Multi-Volt/GG-PrintableMagnets/Data/Plots/10percent_trial1/10percent_trial1_vector_field_scalar.png

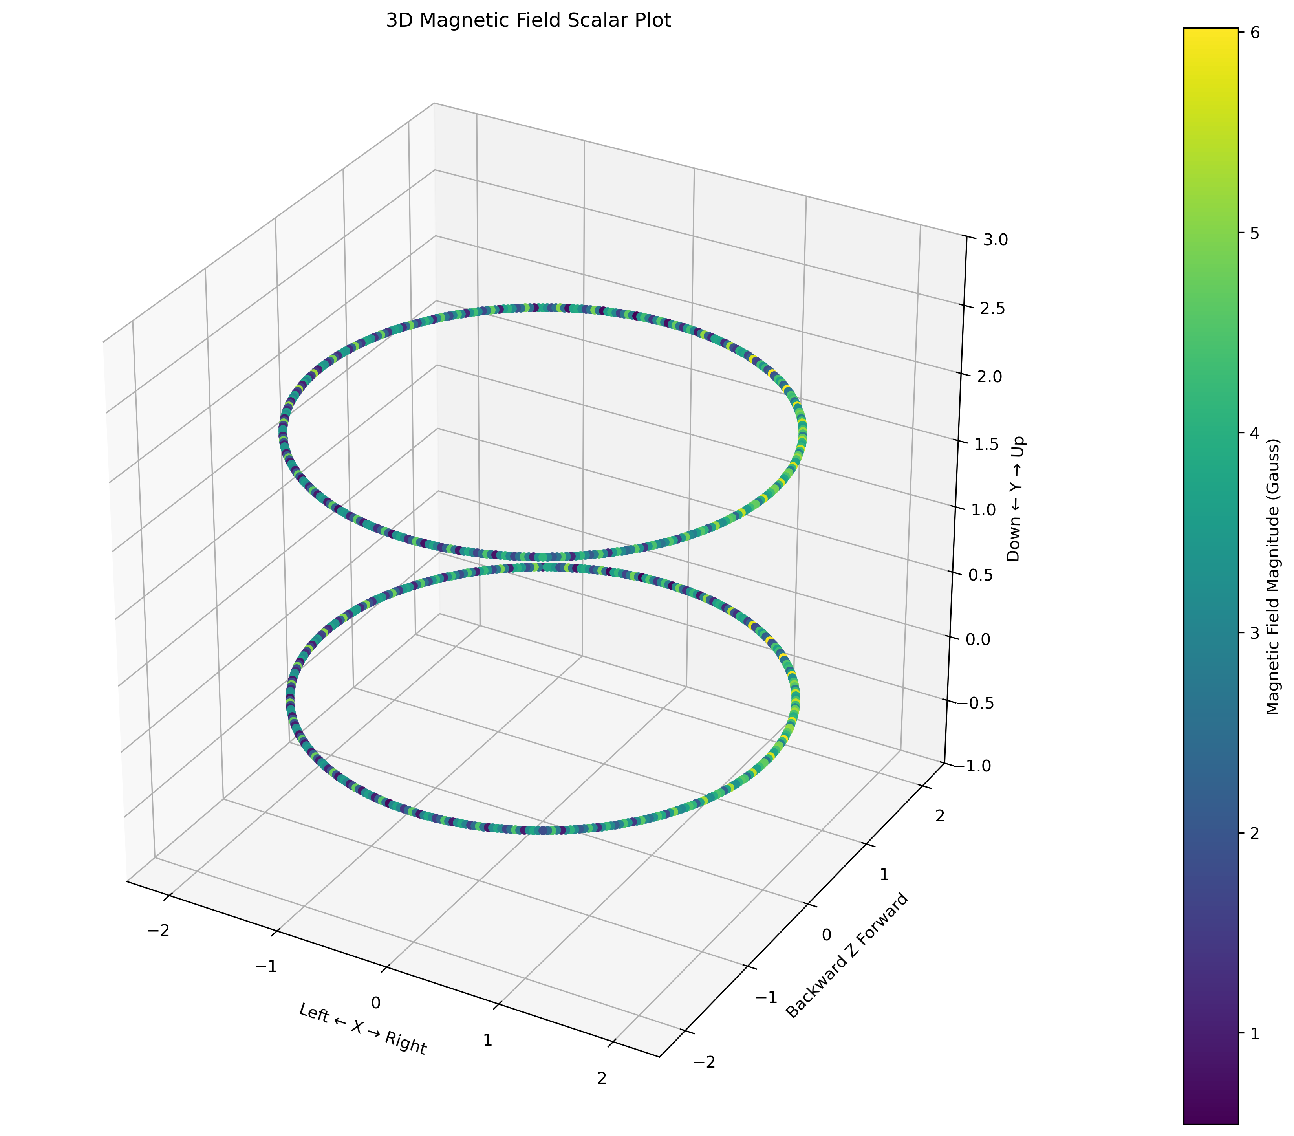
Data/Plots/10percent_trial1/10percent_trial1_vector_field_scalar.png
