Multi-Volt/GG-PrintableMagnets/Data/Plots/10percent_trial1/10percent_trial1_vector_field_true_vector.png

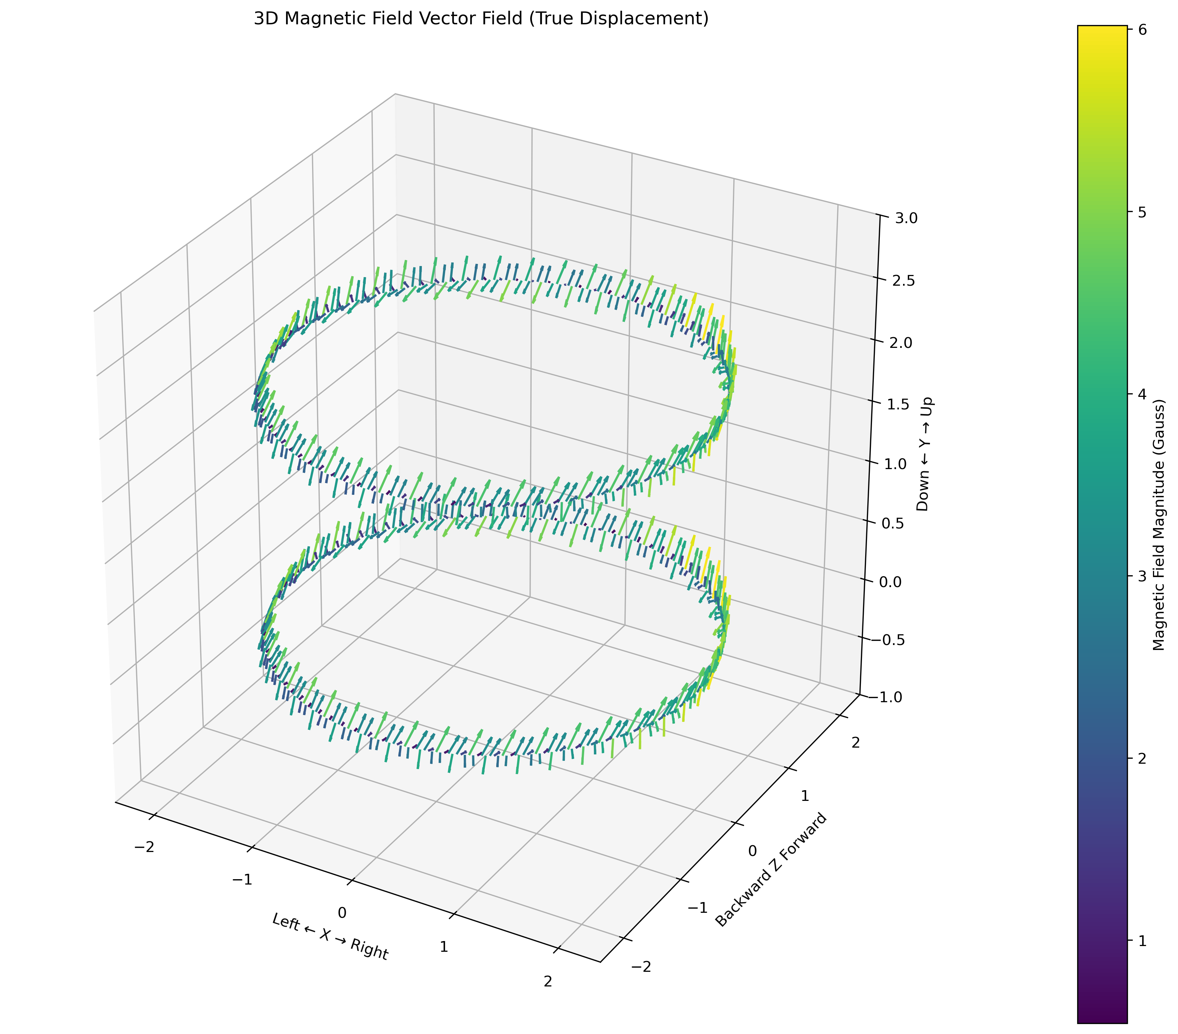
Data/Plots/10percent_trial1/10percent_trial1_vector_field_true_vector.png
