Multi-Volt/GG-PrintableMagnets/Data/Plots/10percent_trial2/10percent_trial2_vector_field_mesh_shrink.png

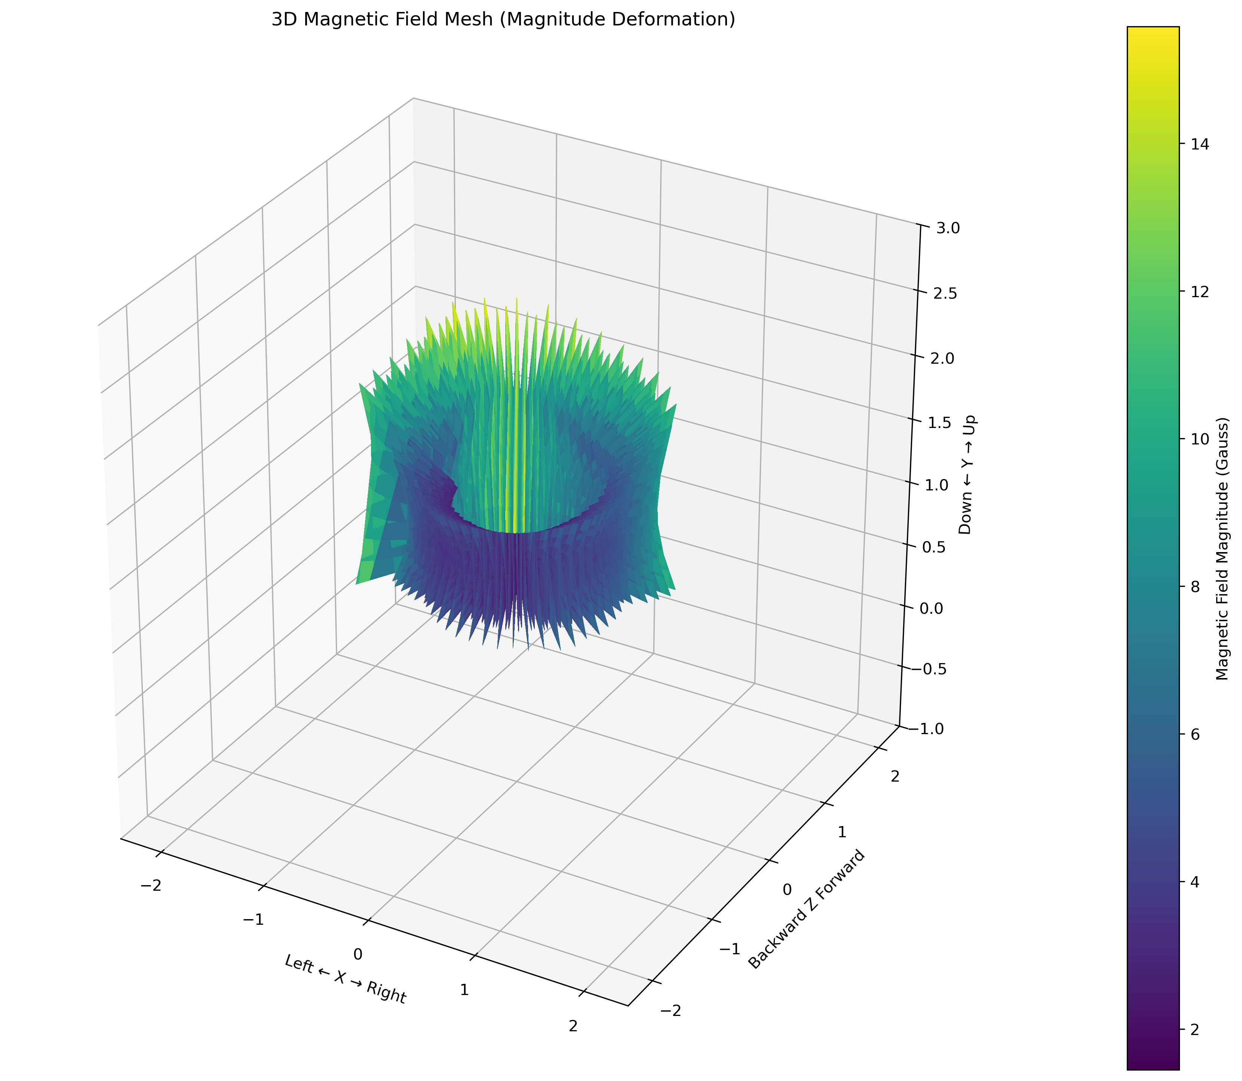
Data/Plots/10percent_trial2/10percent_trial2_vector_field_mesh_shrink.png
