Multi-Volt/GG-PrintableMagnets/Data/Plots/10percent_trial2/10percent_trial2_vector_field_true_vector.png

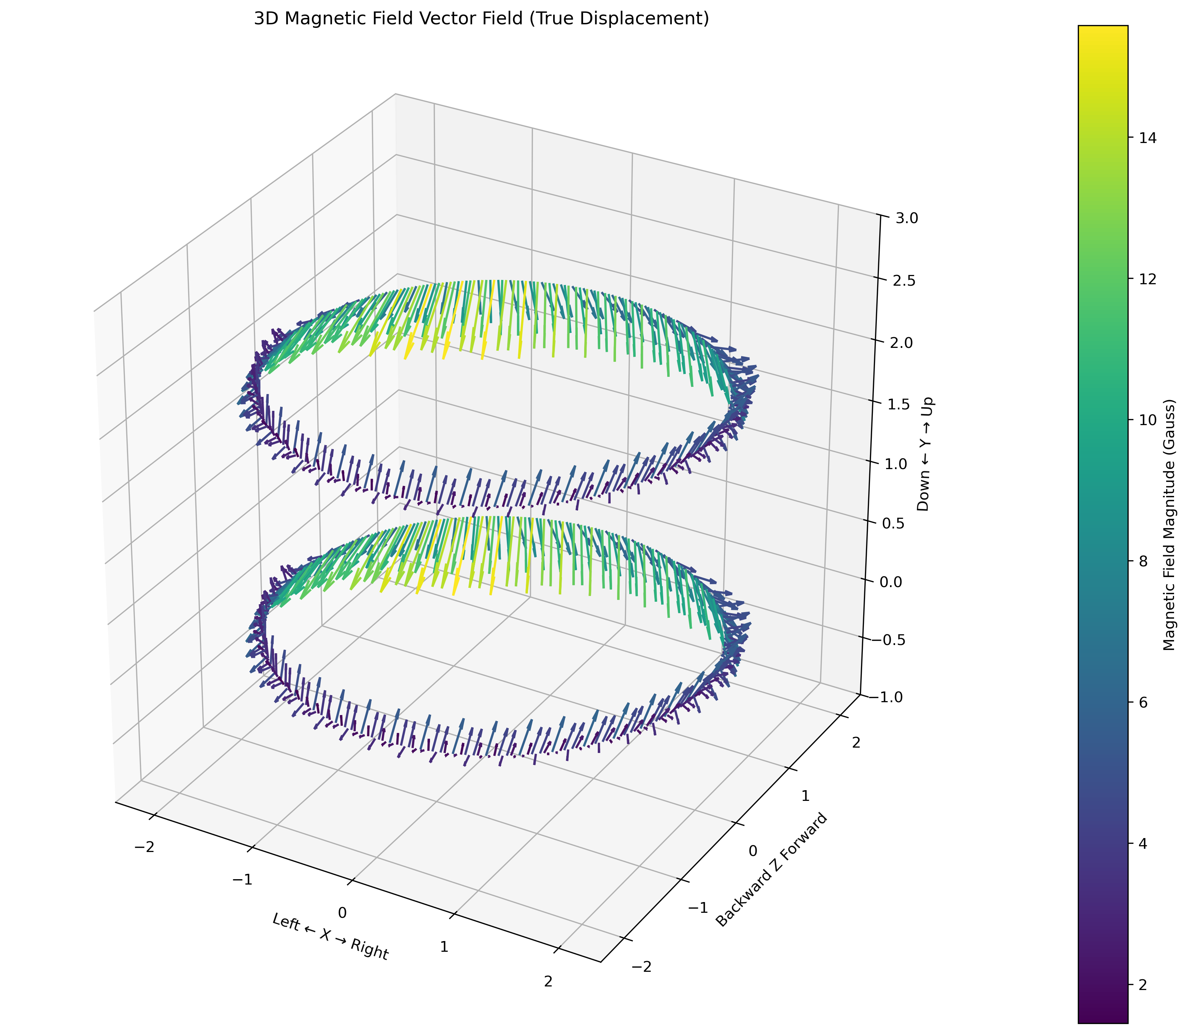
Data/Plots/10percent_trial2/10percent_trial2_vector_field_true_vector.png
