Multi-Volt/GG-PrintableMagnets/Data/Plots/10percent_trial5/10percent_trial5_vector_field_scalar.png

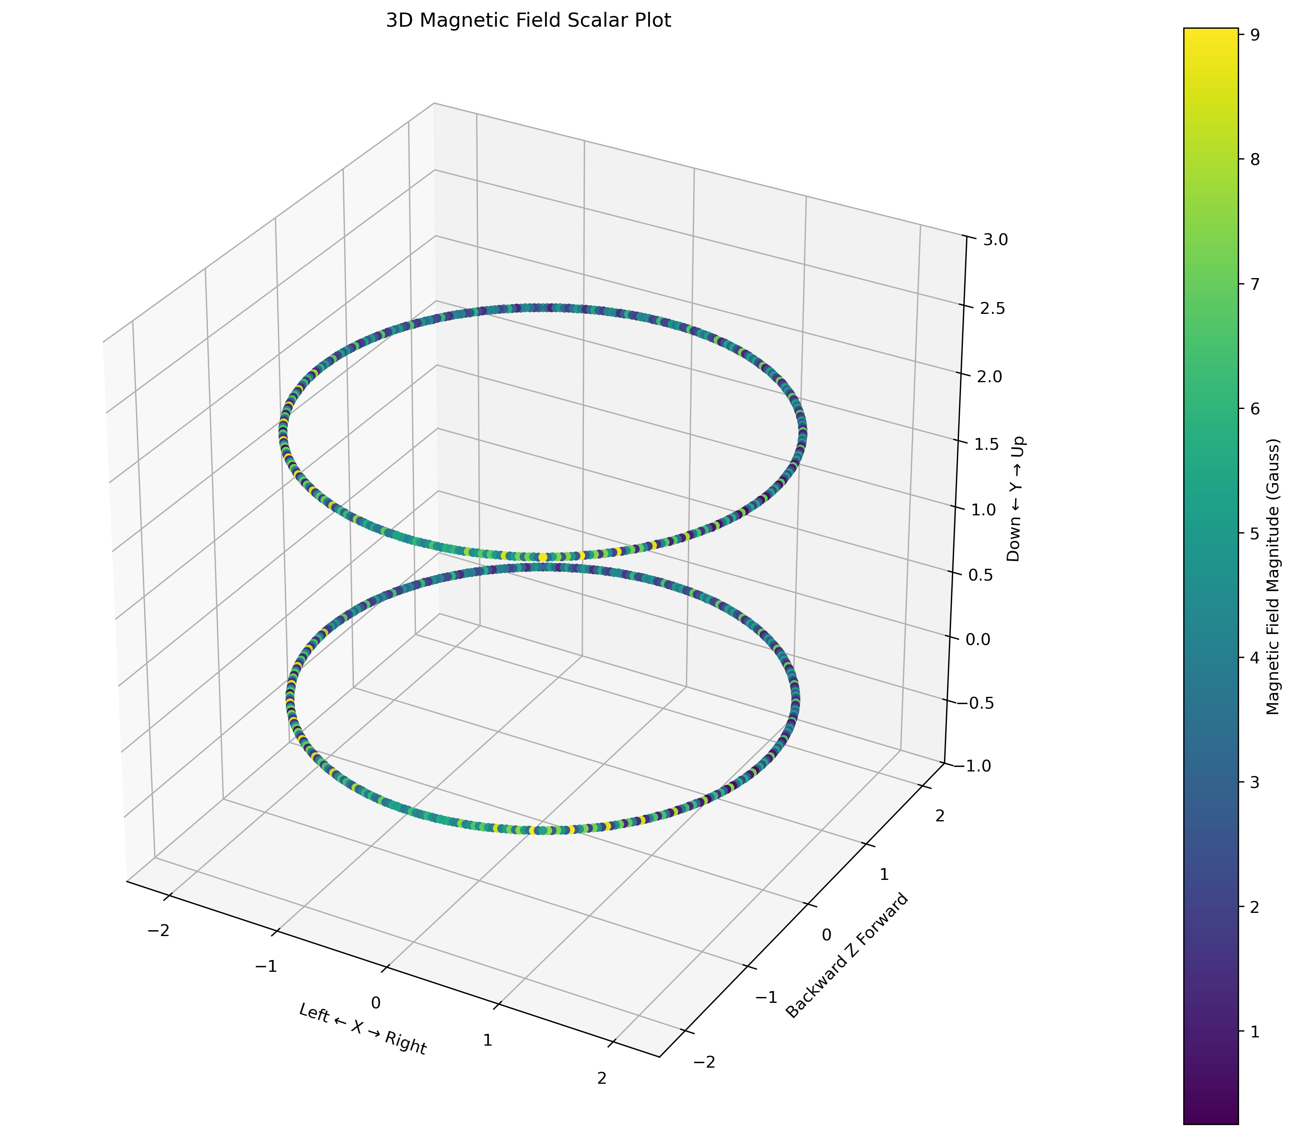
Data/Plots/10percent_trial5/10percent_trial5_vector_field_scalar.png
