Multi-Volt/GG-PrintableMagnets/Data/Plots/10percent_trial5/10percent_trial5_vector_field_true_vector.png

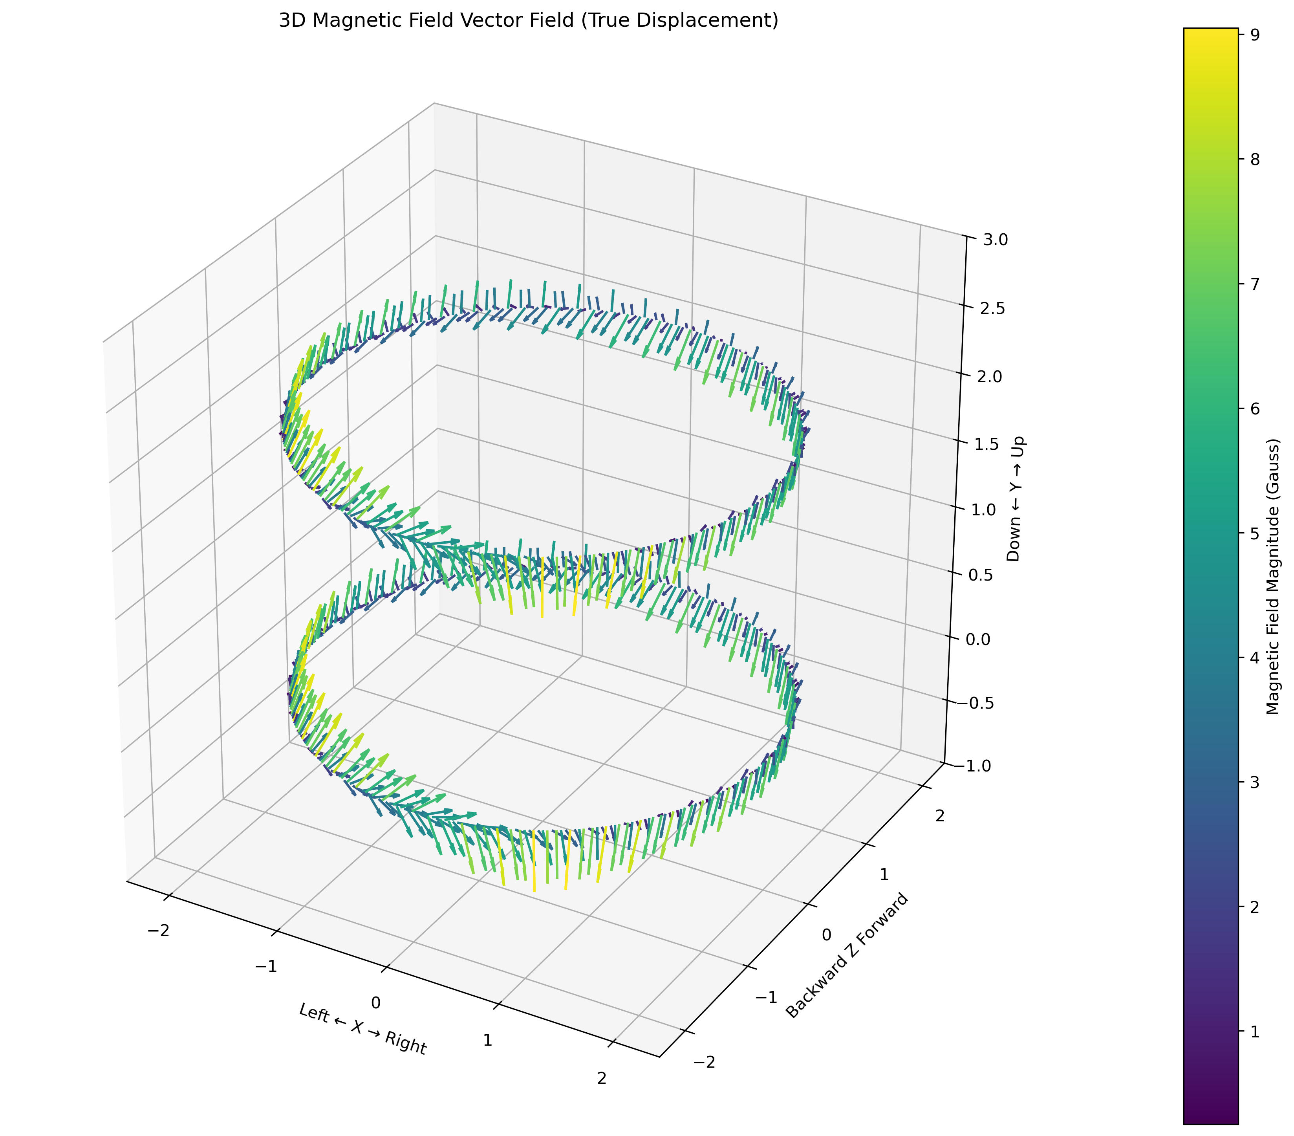
Data/Plots/10percent_trial5/10percent_trial5_vector_field_true_vector.png
