Multi-Volt/GG-PrintableMagnets/Data/Plots/30percent_trial1/30percent_trial1_vector_field_true_vector.png

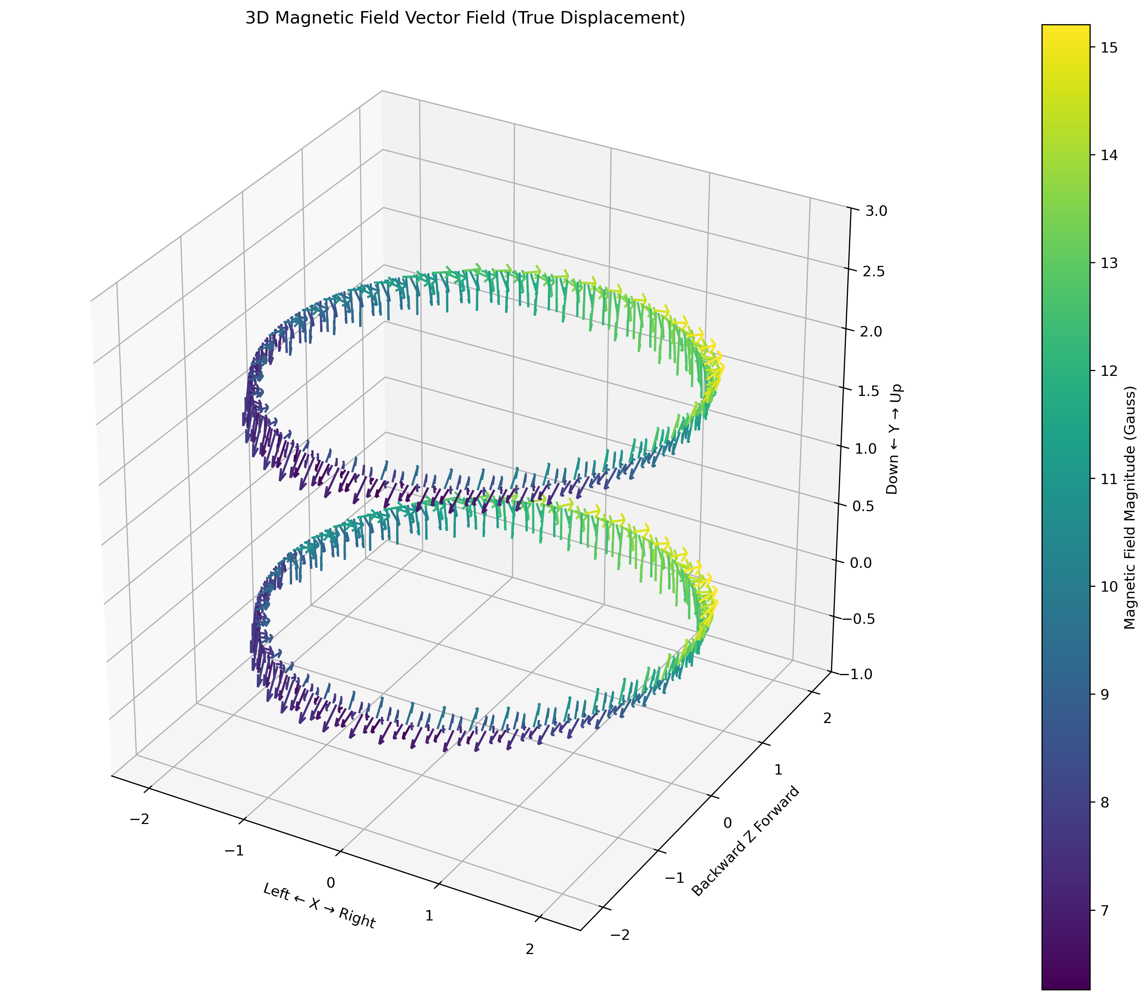
Data/Plots/30percent_trial1/30percent_trial1_vector_field_true_vector.png
