Multi-Volt/GG-PrintableMagnets/Data/Plots/30percent_trial2/30percent_trial2_vector_field_true_vector.png

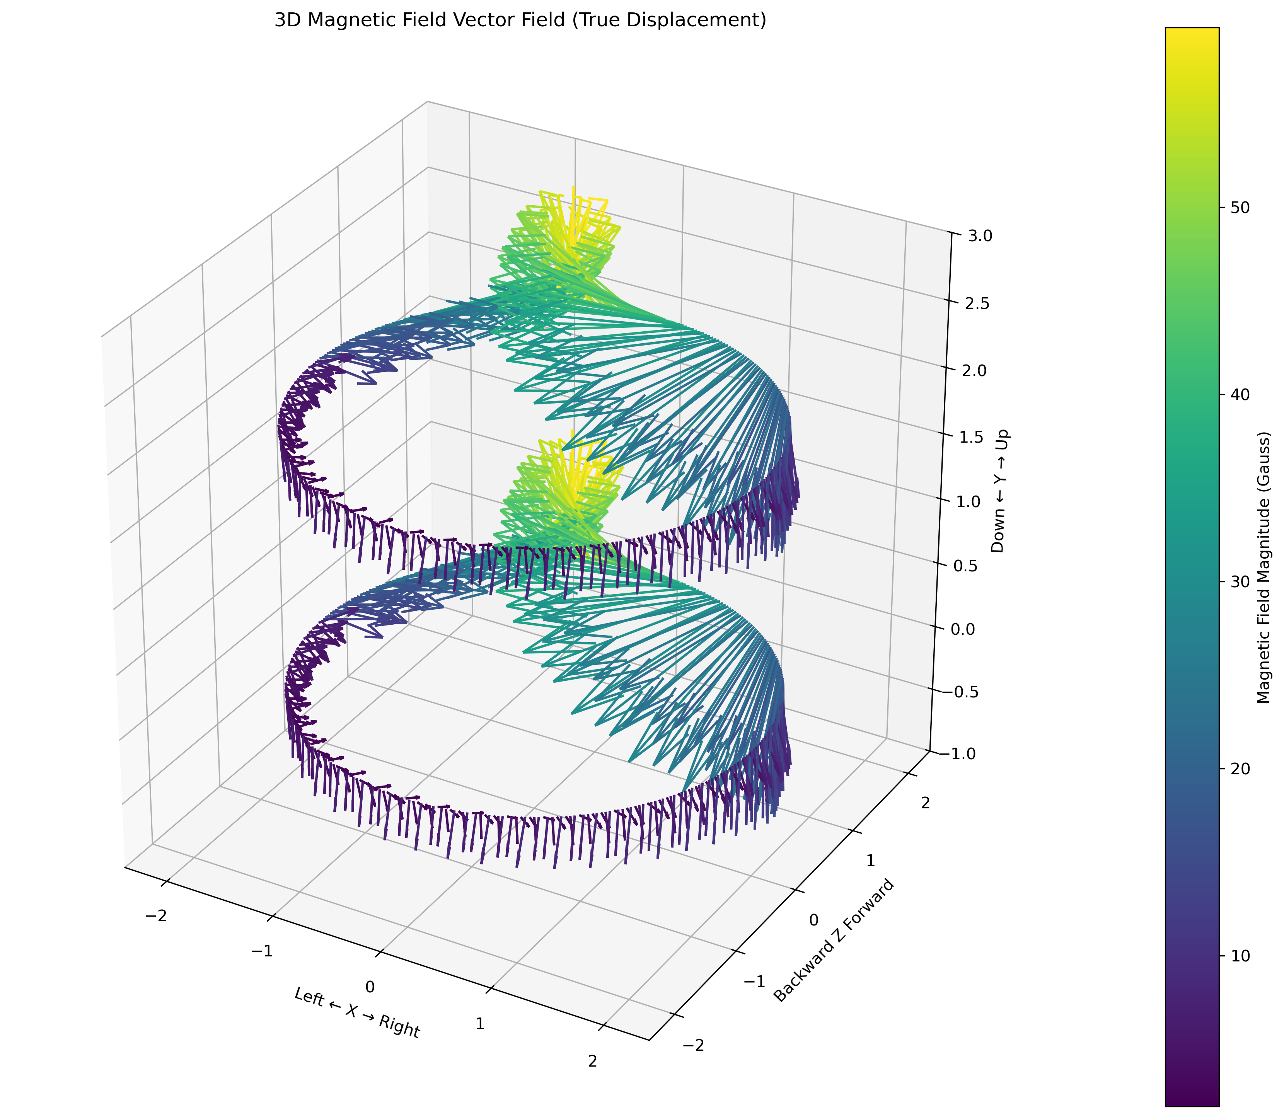
Data/Plots/30percent_trial2/30percent_trial2_vector_field_true_vector.png
