Multi-Volt/GG-PrintableMagnets/Data/Plots/30percent_trial3/30percent_trial3_vector_field_mesh_shrink.png

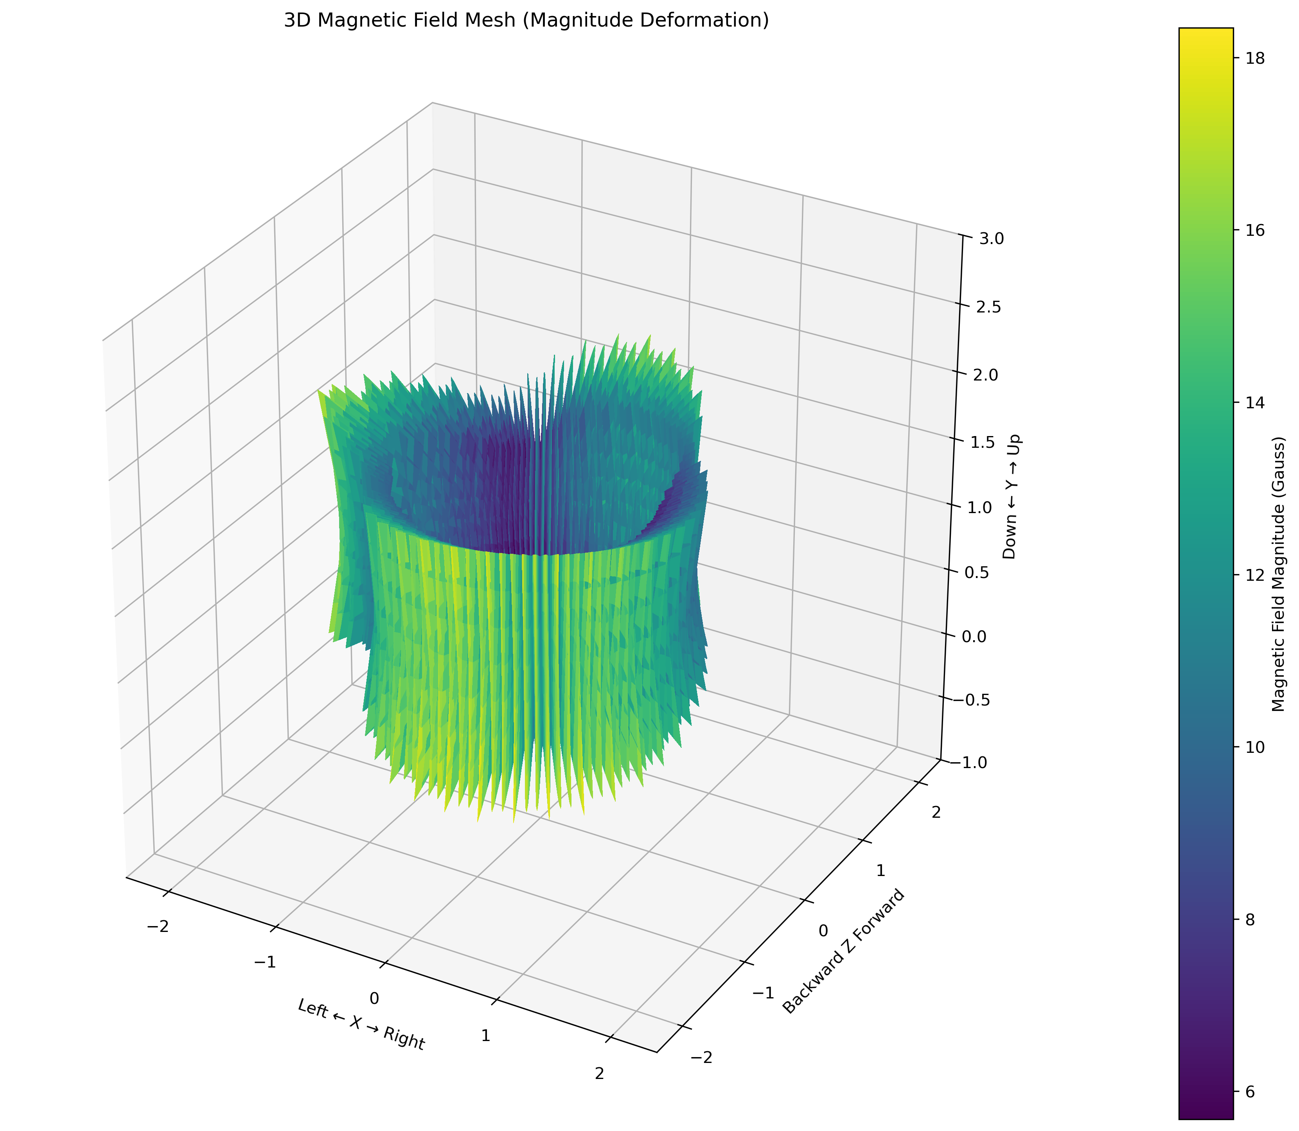
Data/Plots/30percent_trial3/30percent_trial3_vector_field_mesh_shrink.png
