Multi-Volt/GG-PrintableMagnets/Data/Plots/50percent_trial1/50percent_trial1_vector_field_scalar.png

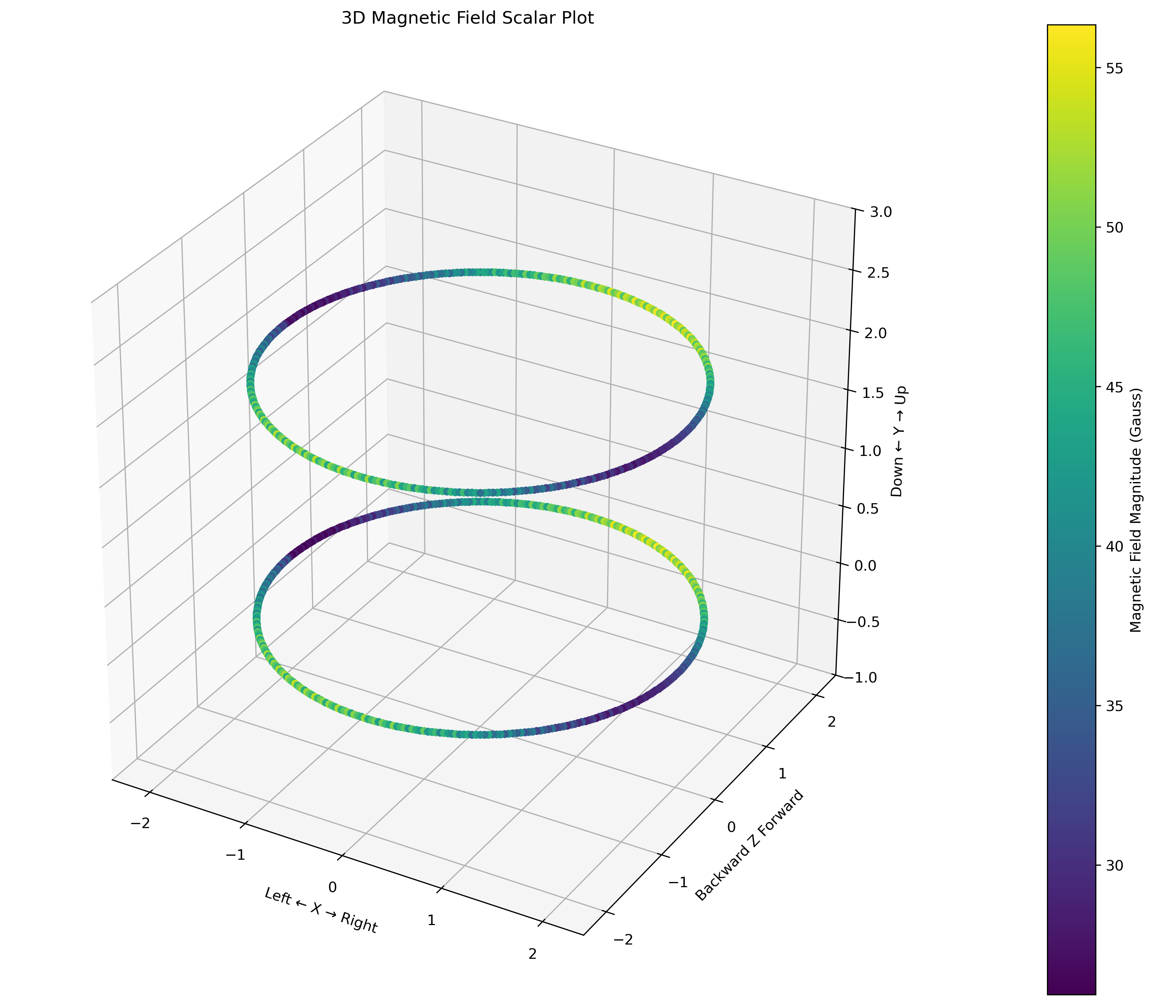
Data/Plots/50percent_trial1/50percent_trial1_vector_field_scalar.png
