Multi-Volt/GG-PrintableMagnets/Data/Plots/50percent_trial1/50percent_trial1_vector_field_true_vector.png

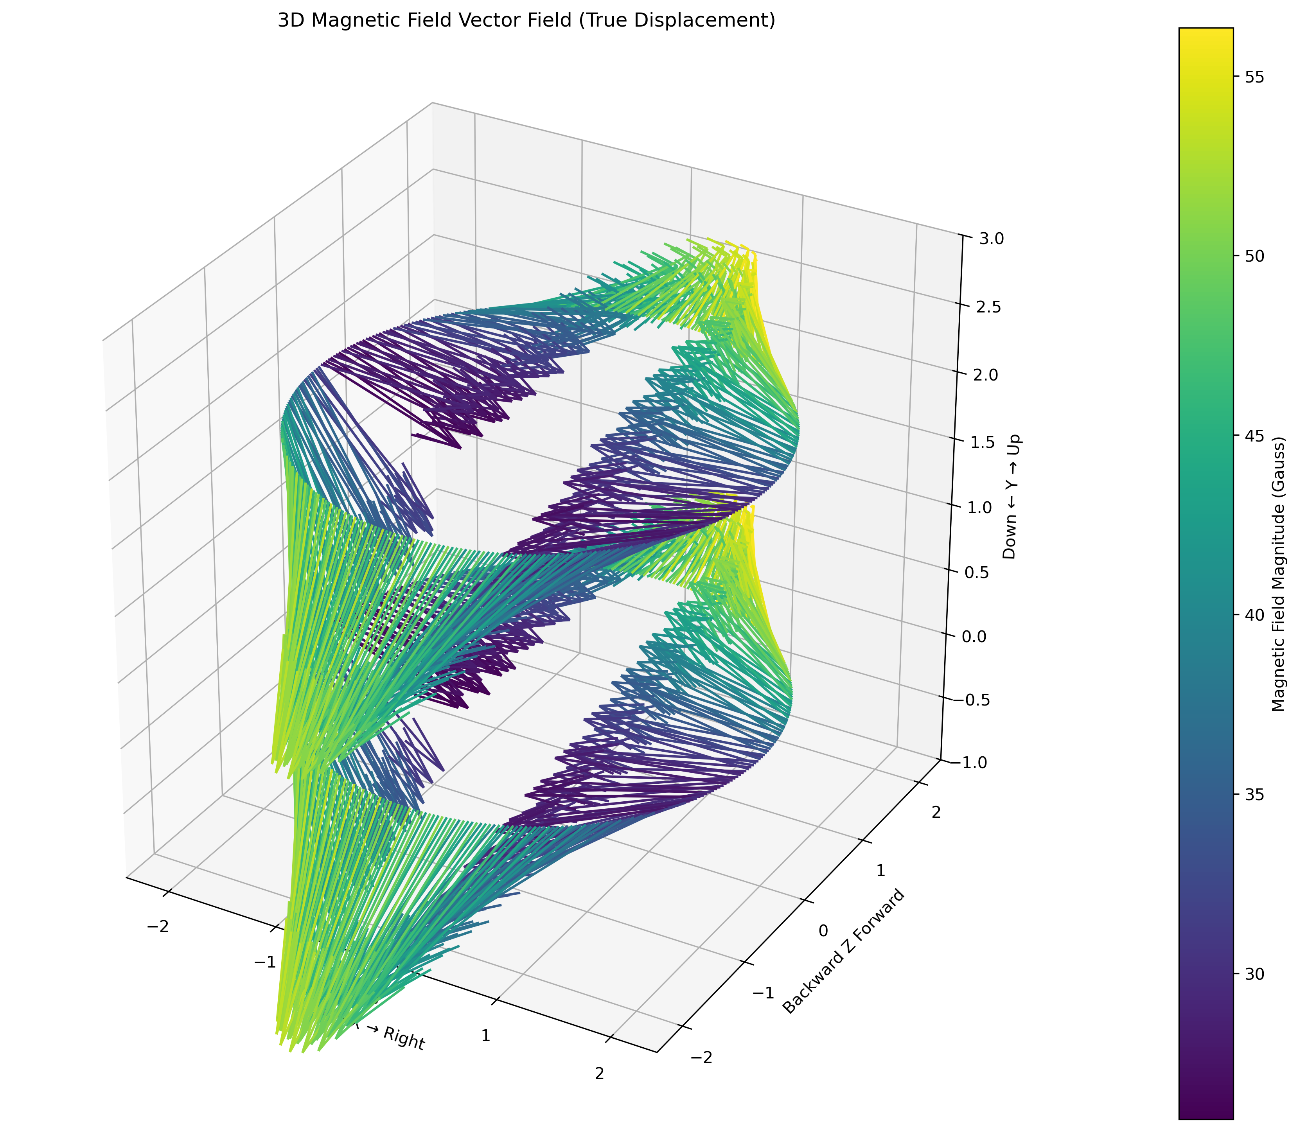
Data/Plots/50percent_trial1/50percent_trial1_vector_field_true_vector.png
