Multi-Volt/GG-PrintableMagnets/Data/Plots/50percent_trial2/50percent_trial2_vector_field_true_vector.png

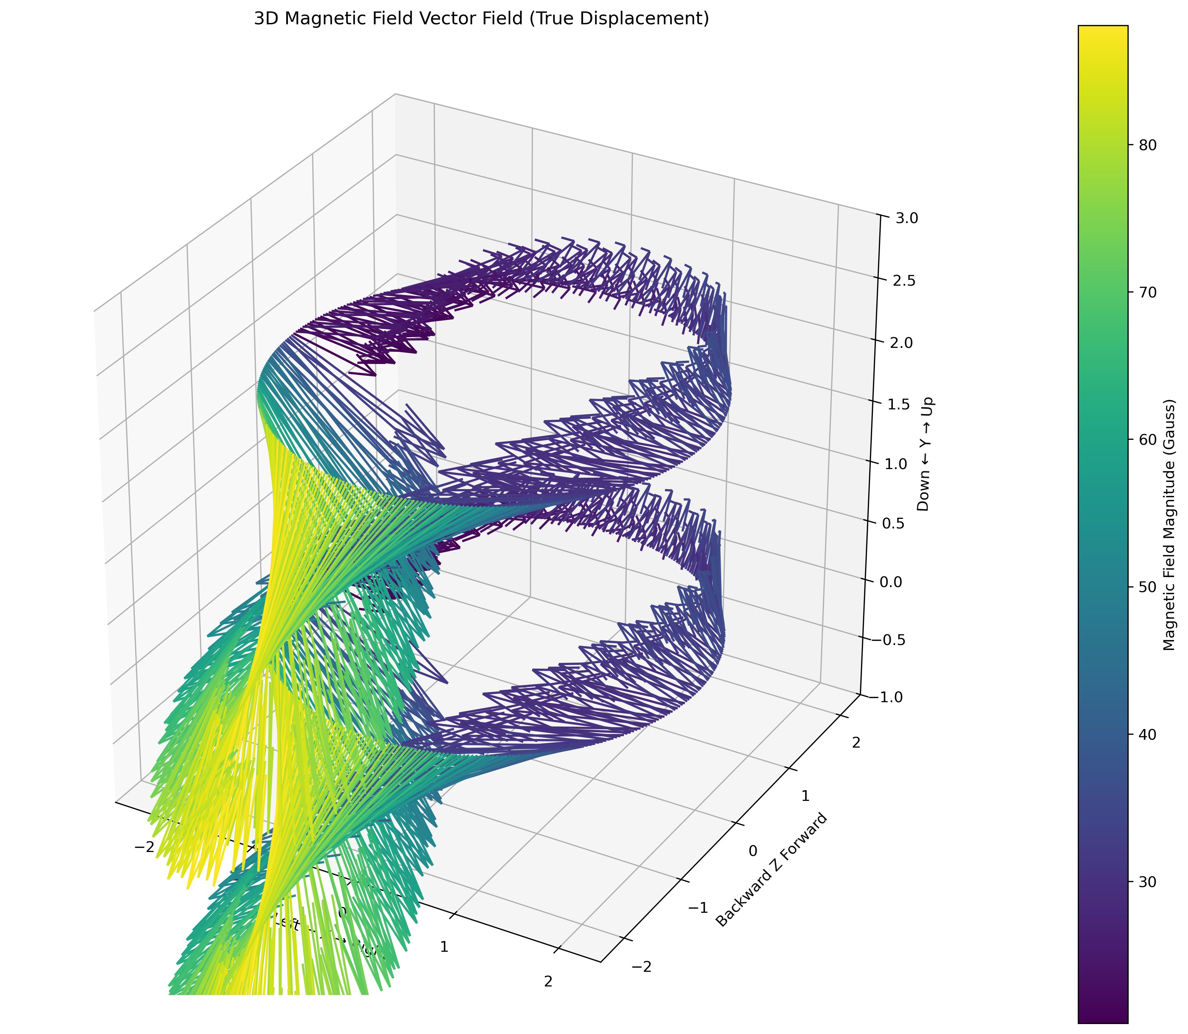
Data/Plots/50percent_trial2/50percent_trial2_vector_field_true_vector.png
