Multi-Volt/GG-PrintableMagnets/Data/Plots/50percent_trial3/50percent_trial3_vector_field_true_vector.png

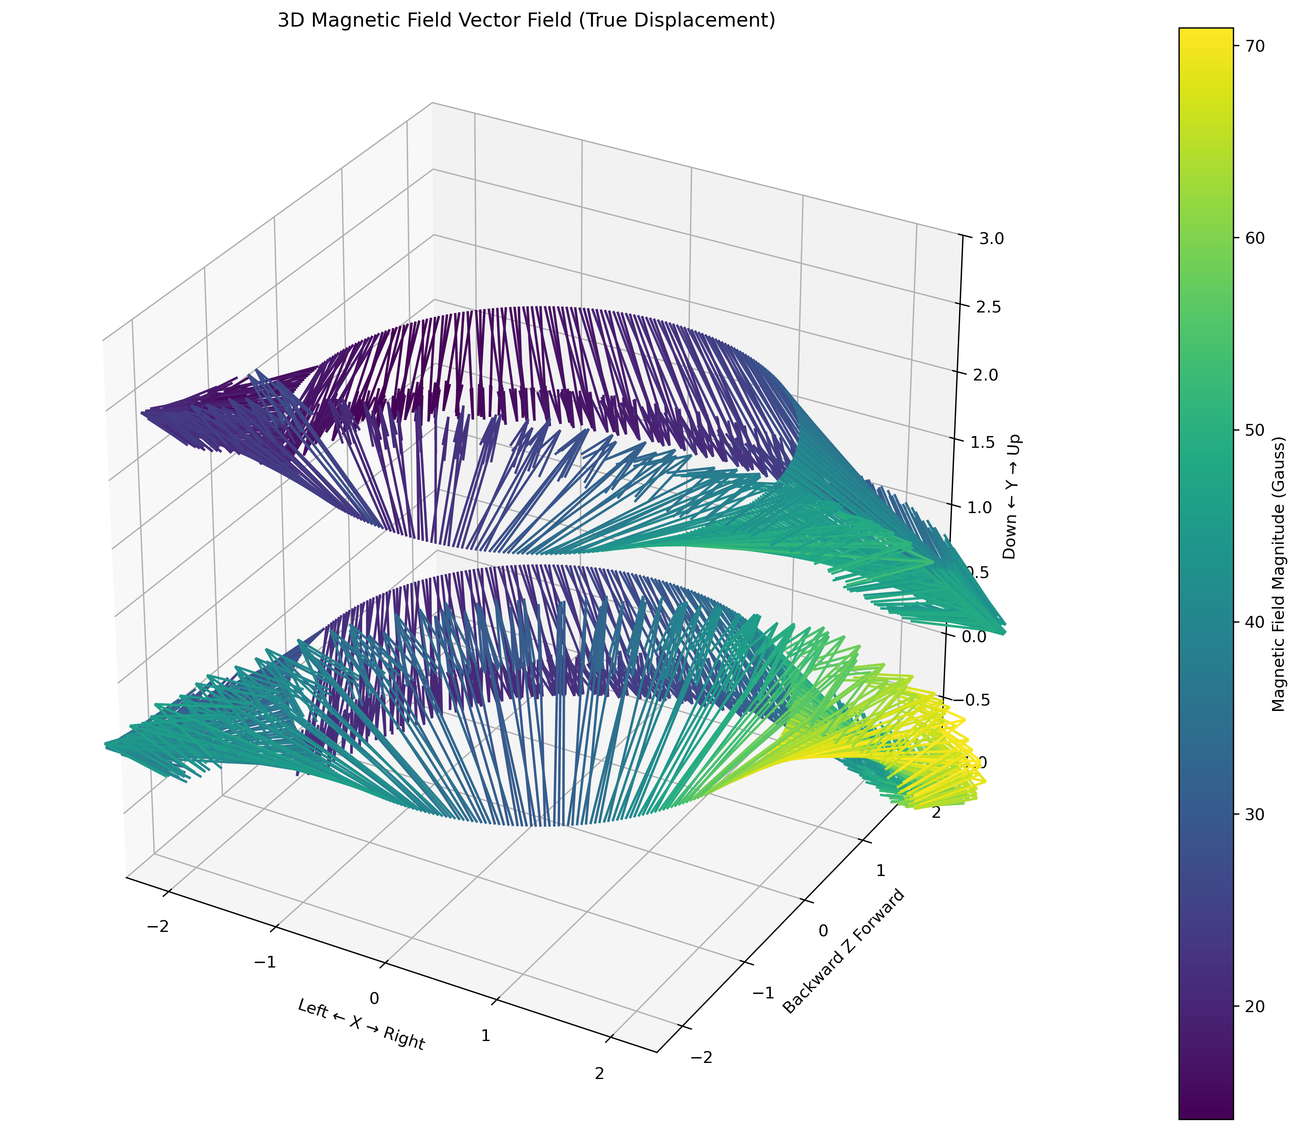
Data/Plots/50percent_trial3/50percent_trial3_vector_field_true_vector.png
