Multi-Volt/GG-PrintableMagnets/Data/Plots/50percent_trial4/50percent_trial4_vector_field_true_vector.png

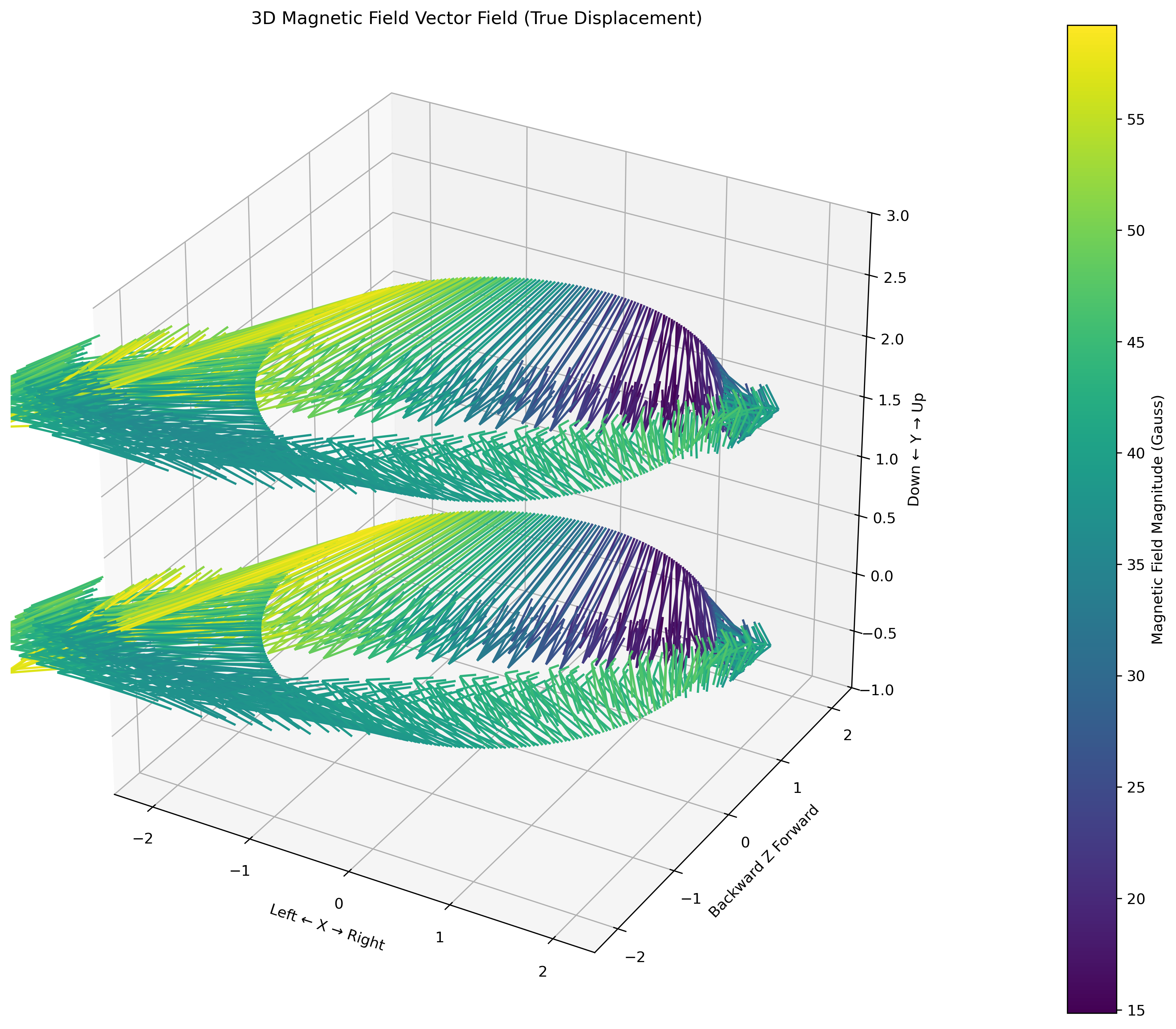
Data/Plots/50percent_trial4/50percent_trial4_vector_field_true_vector.png
