Multi-Volt/GG-PrintableMagnets/Data/Plots/50percent_trial5/50percent_trial5_vector_field_unit_vector.png

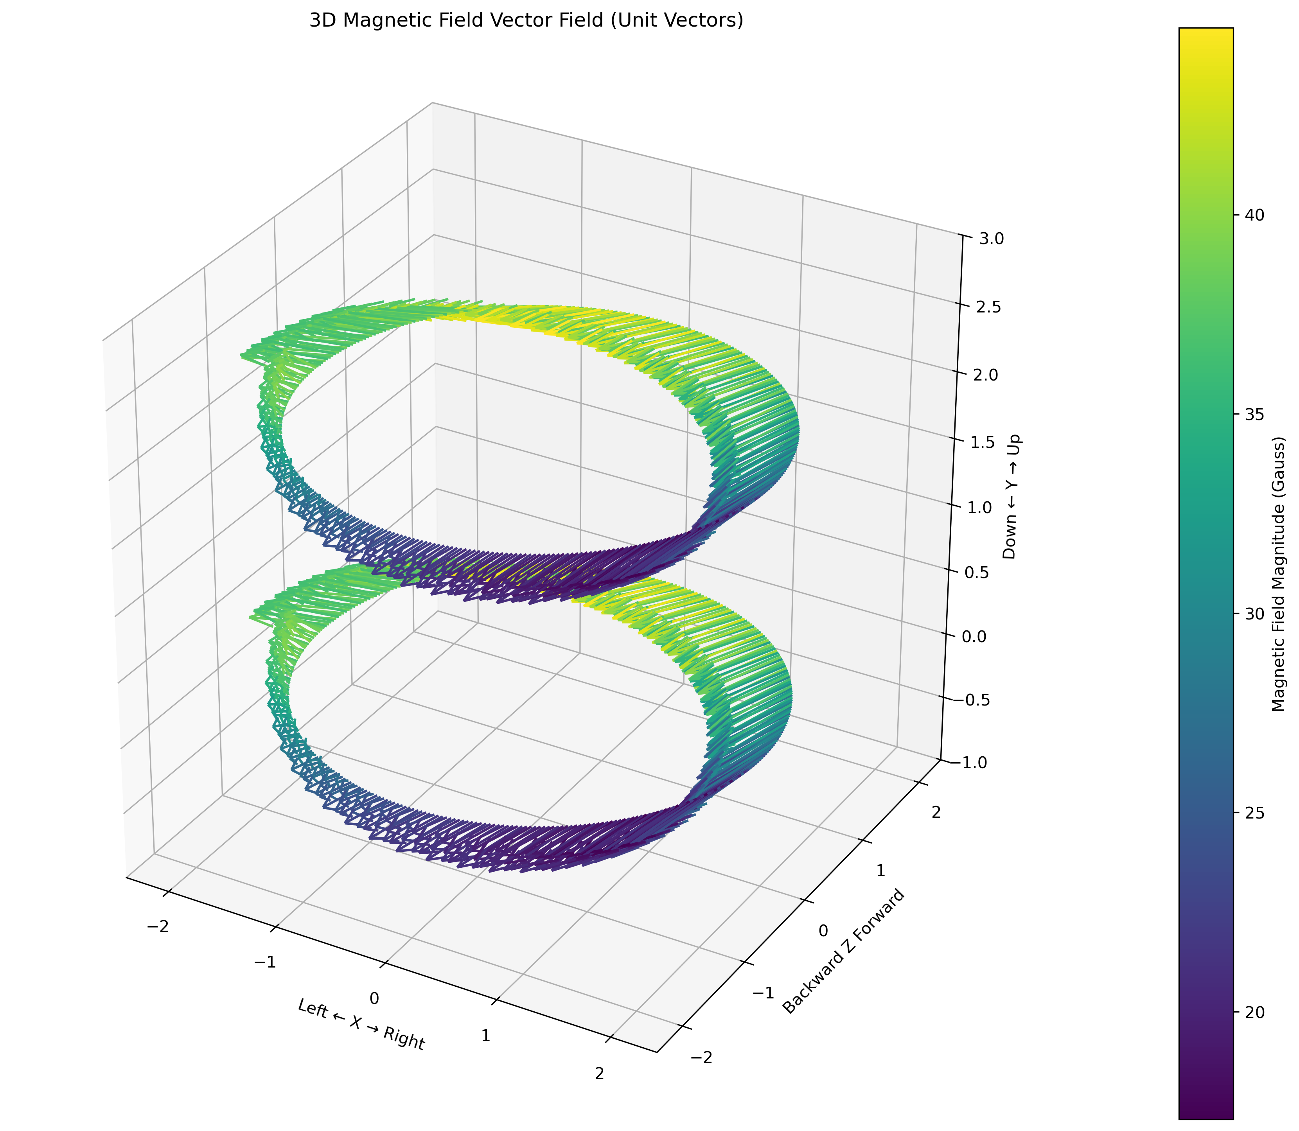
Data/Plots/50percent_trial5/50percent_trial5_vector_field_unit_vector.png
