Multi-Volt/GG-PrintableMagnets/Data/Plots/reference_magnet/reference_magnet_vector_field_scalar.png

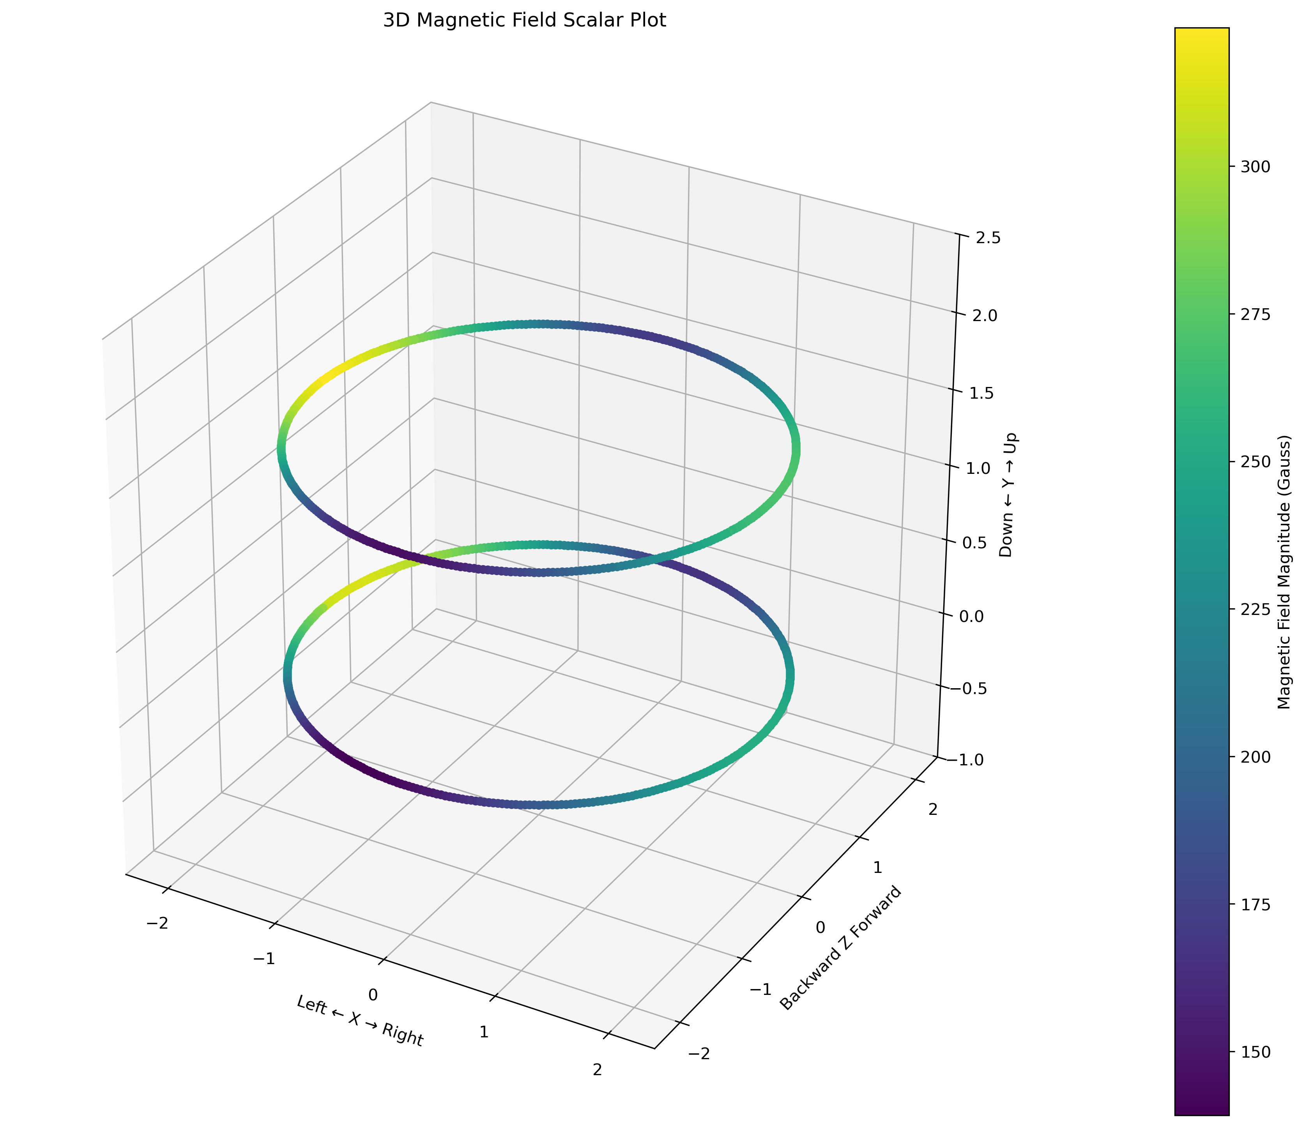
Data/Plots/reference_magnet/reference_magnet_vector_field_scalar.png
